chris-heo/pirozeda/firmware/ProzedaReader/simpleio.h

/*
 * SimpleIO.h
 *
 * Created: 09.02.2014 21:55:54
 *  Author: Chris
 */ 


#ifndef SIMPLEIO_H_
#define SIMPLEIO_H_

#include <avr/io.h>

//usage: #define MyPin   IOPIN(B, 2)

#define IOPIN(port, pin) port, pin

#define __IOPIN_PORT(port, pin) PORT##port
#define __IOPIN_DDR(port, pin) DDR##port
#define __IOPIN_PIN(port, pin) PIN##port
#define __IOPIN_MASK(port, pin) (1<<pin)

#define __IOPIN_O(port, pin) do { DDR##port |=  (1<<pin); } while(0)
#define __IOPIN_I(port, pin) do { DDR##port &= (uint8_t)~(1<<pin); } while(0)

#define __IOPIN_H(port, pin) do { PORT##port |=  (1<<pin); } while(0)
#define __IOPIN_L(port, pin) do { PORT##port &= (uint8_t)~(1<<pin); } while(0)
#define __IOPIN_T(port, pin) do { PORT##port ^=  (1<<pin); } while(0)

#define __IOPIN_V(port, pin) (PIN##port & (1<<pin))

#define IOPIN_PORT(x) __IOPIN_PORT(x, 0)
#define IOPIN_DDR(x)  __IOPIN_DDR(x, 0)
#define IOPIN_PIN(x)  __IOPIN_PIN(x, 0)
#define IOPIN_MASK(x) __IOPIN_MASK(x)


#define IOPIN_O(x) __IOPIN_O(x)
#define IOPIN_I(x) __IOPIN_I(x)

#define IOPIN_H(x) __IOPIN_H(x)
#define IOPIN_L(x) __IOPIN_L(x)
#define IOPIN_T(x) __IOPIN_T(x)

#define IOPIN_V(x) __IOPIN_V(x)

#endif /* SIMPLEIO_H_ */
